stevecorey/g9/poster/20181204_125109.jpg

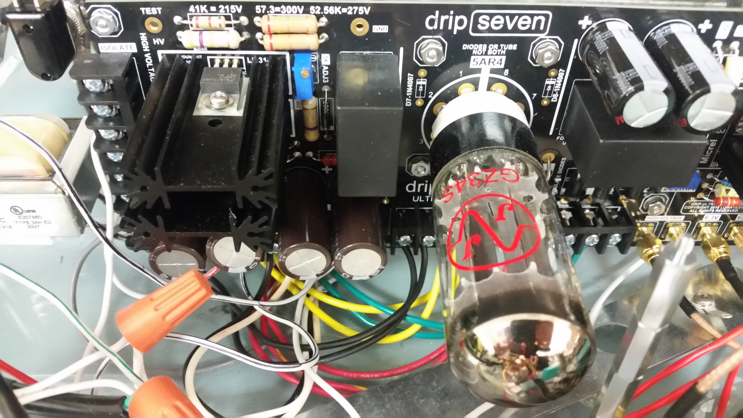
poster/20181204_125109.jpg
