stevecorey/g9/poster/Block%2FFlow (1).png

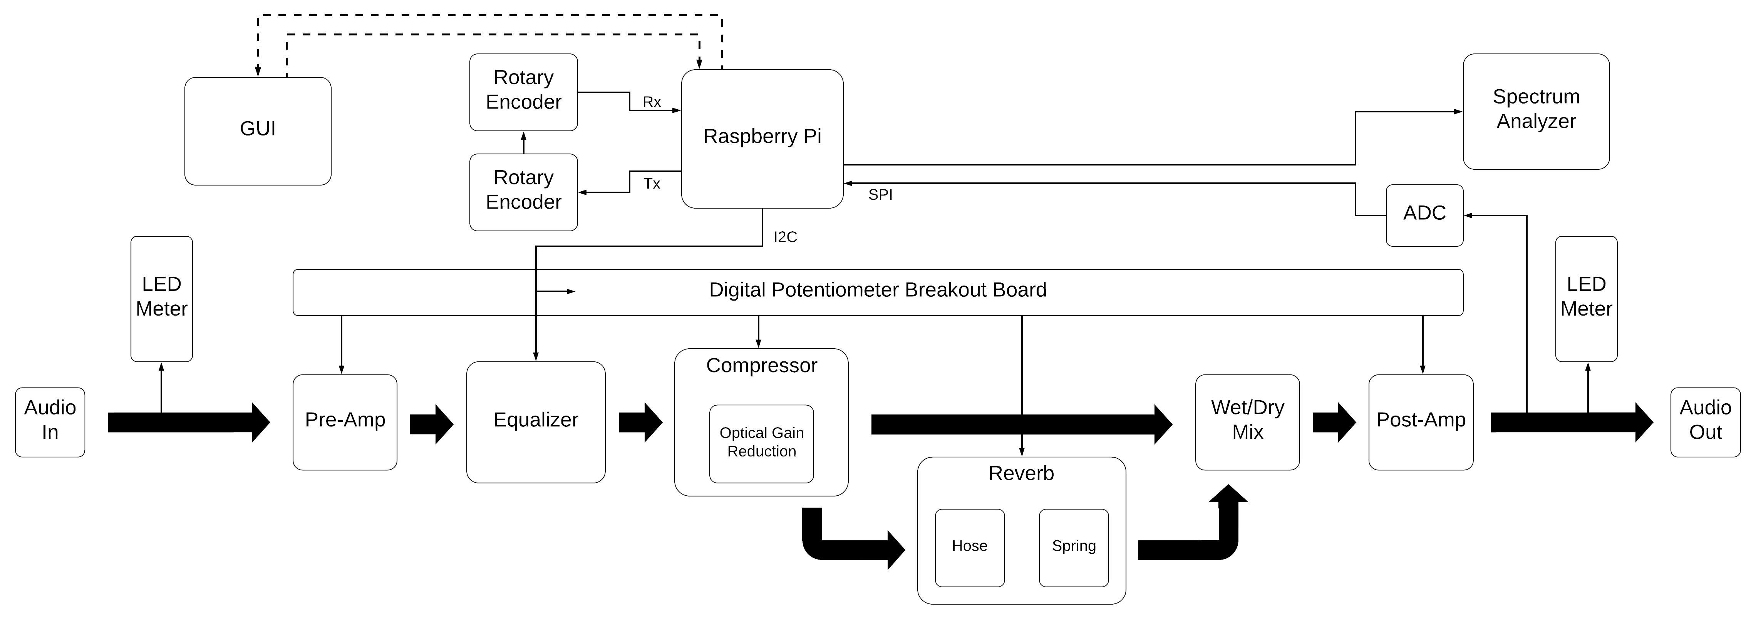
poster/Block%2FFlow (1).png
