stevecorey/g9/poster/meterBoard.jpg

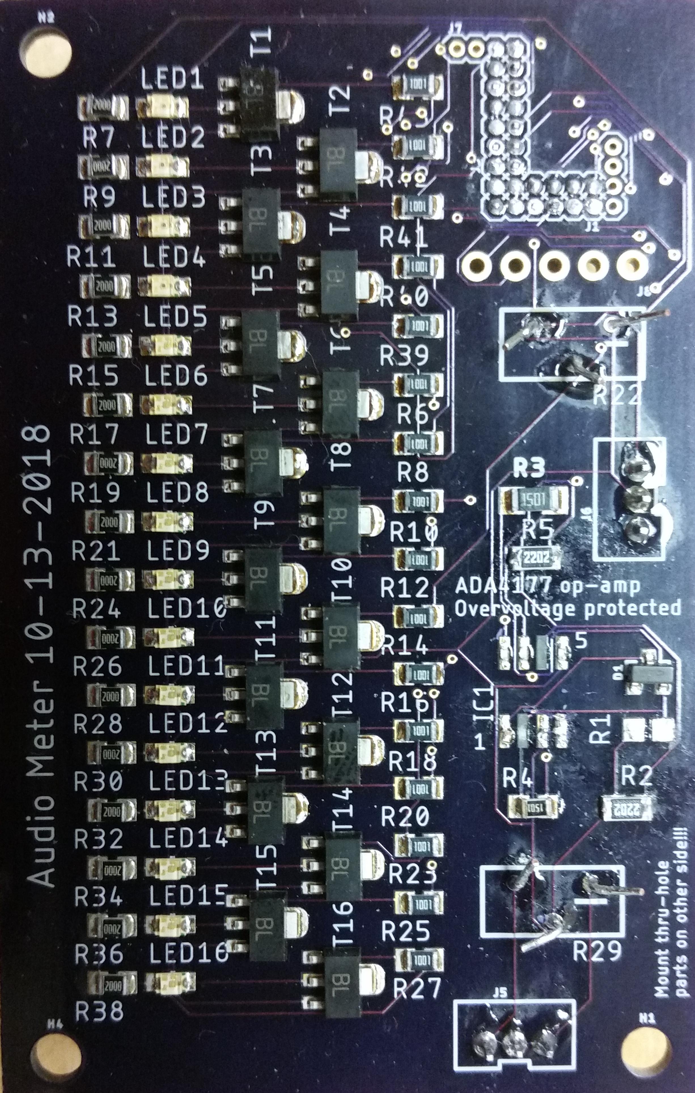
poster/meterBoard.jpg
