stevecorey/g9/poster/photo.jpg

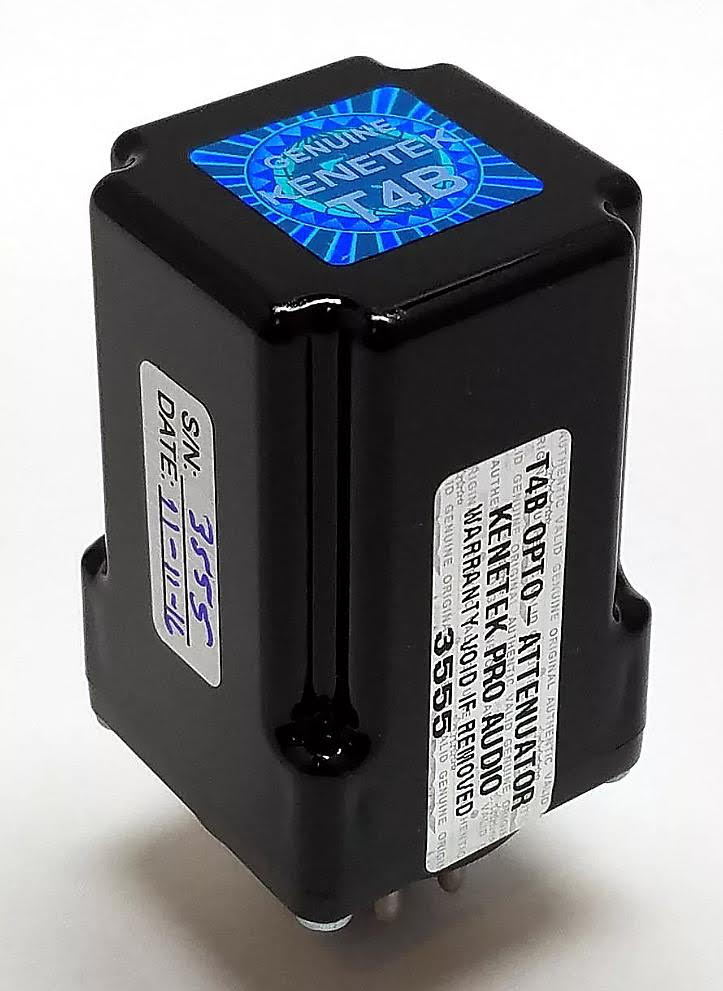
poster/photo.jpg
