stevecorey/g9/poster/reverb.jpg

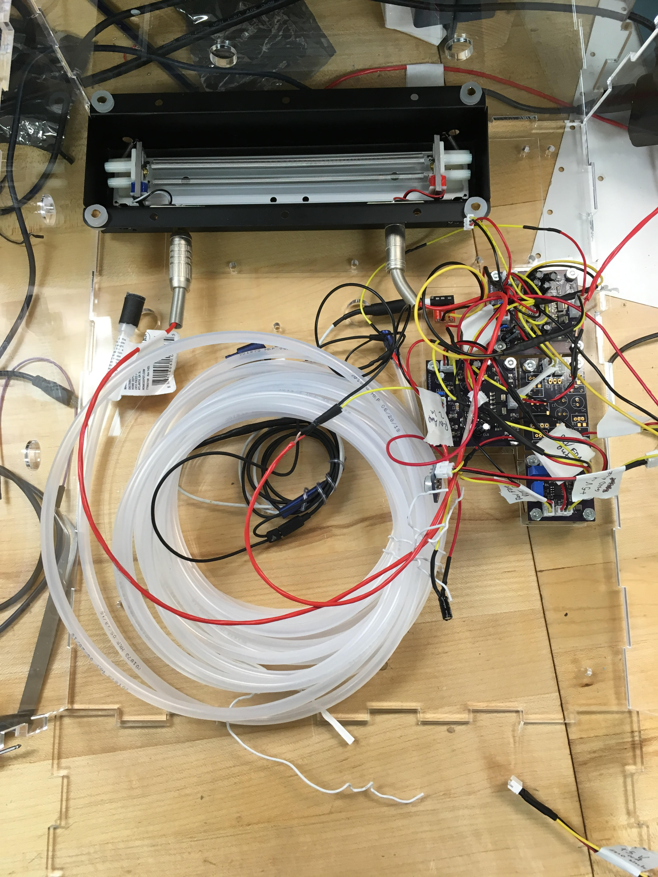
poster/reverb.jpg
