stevecorey/g9/poster/spectrum.png

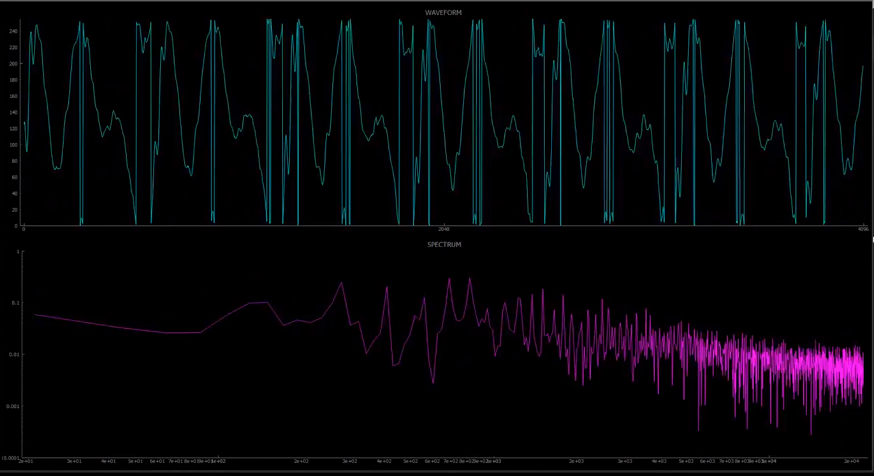
poster/spectrum.png
