stevecorey/g9/proposal/baxandall.png

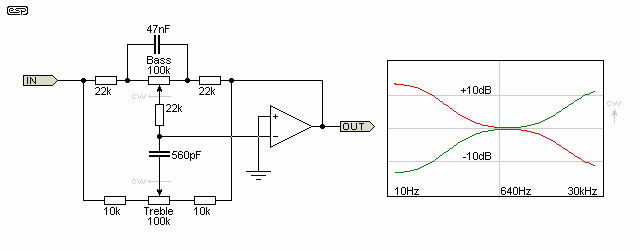
proposal/baxandall.png
