stevecorey/g9/proposal/totalRecall.jpg

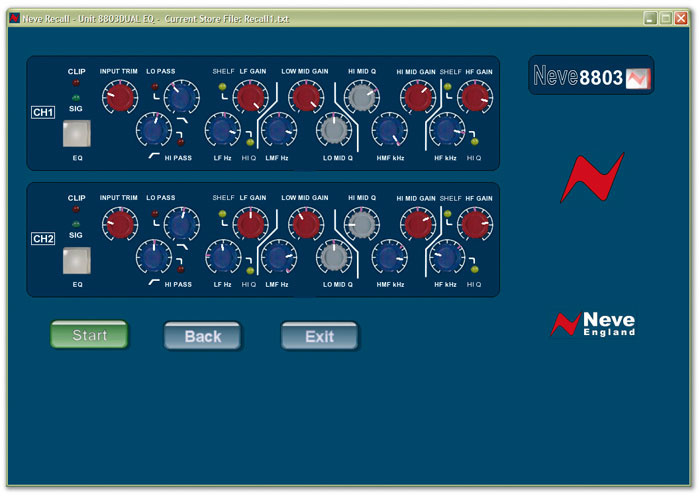
proposal/totalRecall.jpg
