stevecorey/g9/laser/boxTests/A.png

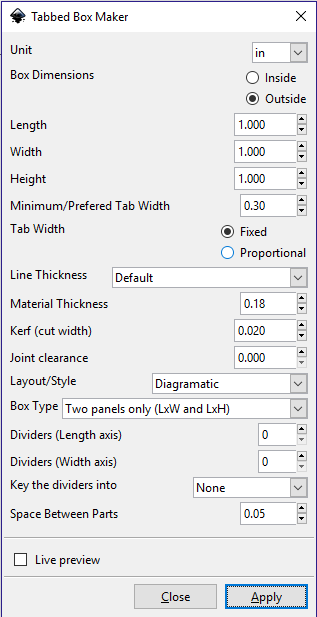
laser/boxTests/A.png
