stevecorey/g9/laser/boxTests/B.png

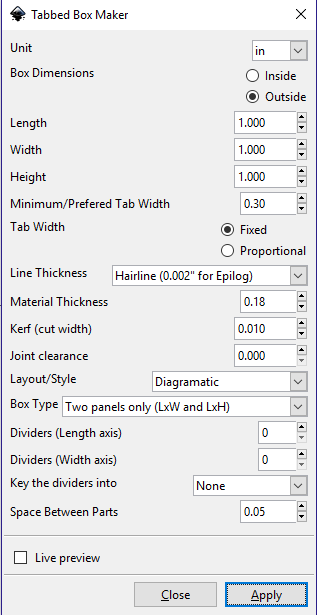
laser/boxTests/B.png
