stevecorey/g9/laser/boxTests/boxes-py-burn-0_3.png

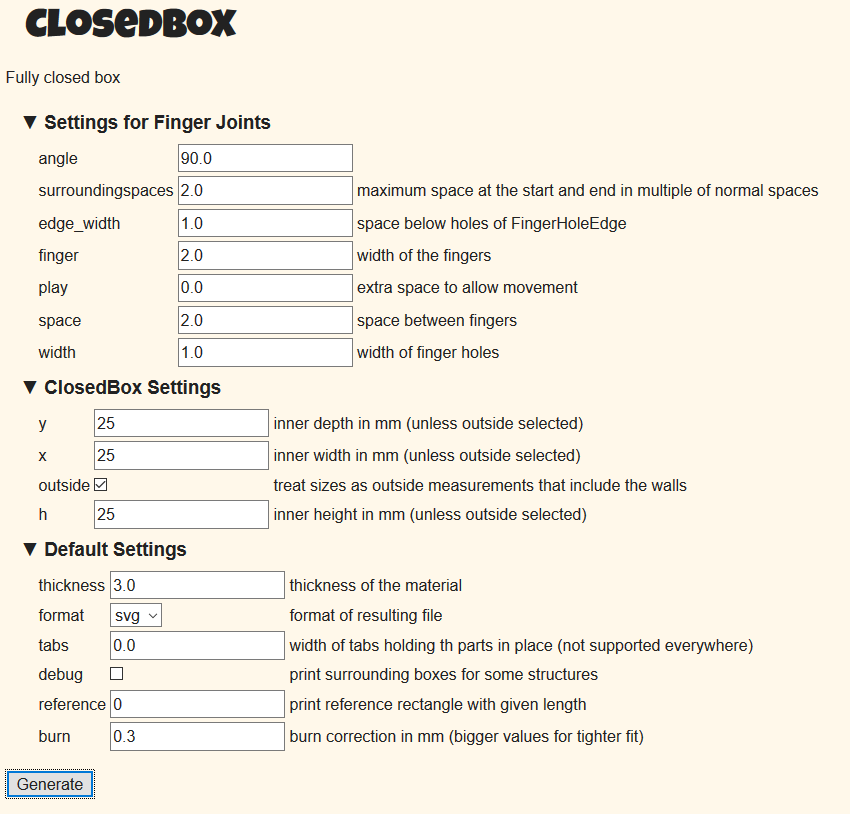
laser/boxTests/boxes-py-burn-0_3.png
