stevecorey/g9/laser/boxTests/D.png

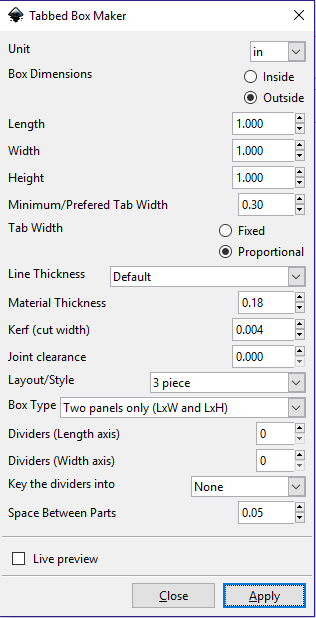
laser/boxTests/D.png
