stevecorey/g9/laser/boxTests/E.png

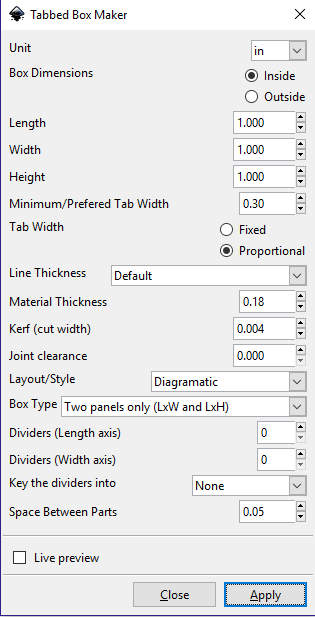
laser/boxTests/E.png
