stevecorey/g9/poster/20181204_122927.jpg

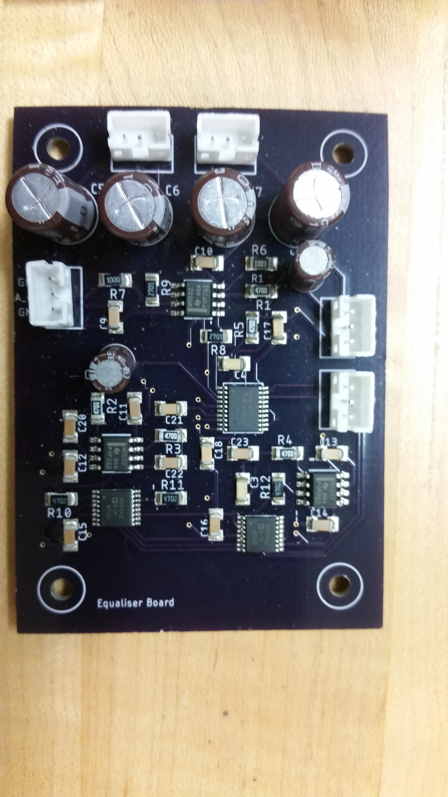
poster/20181204_122927.jpg
