stevecorey/g9/poster/20181204_123032.jpg

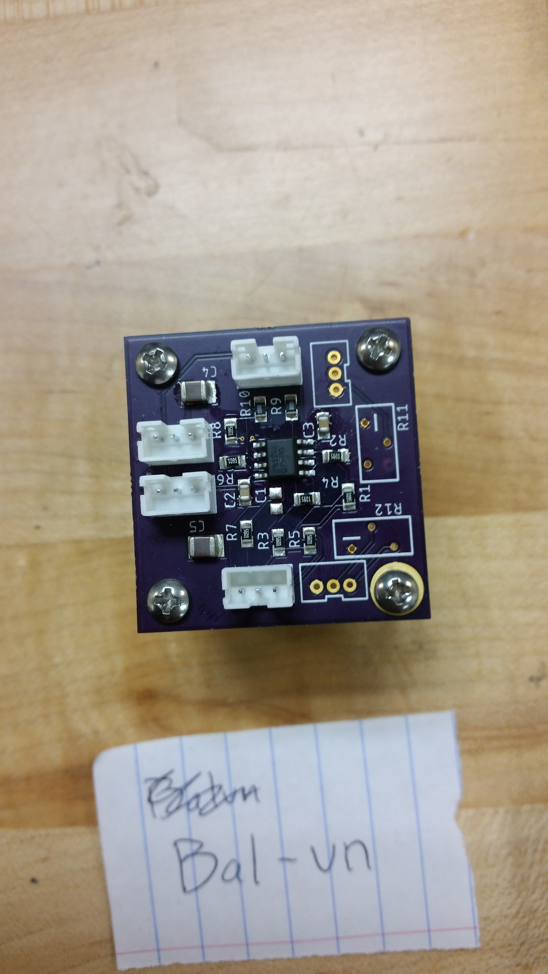
poster/20181204_123032.jpg
